foukemonsterworkshop/filming_accessories/DollyControl/MenuNavigation.ino

void interact_with_menu(MenuState state, int px, int py) {
  switch (state) {
    case MAIN:
      interact_main_menu(px, py);
      break;
    case HOME:
      interact_home_machine_menu(px, py);
      break;
    case JOG:
      interact_jog_menu(px, py);
      break;
    case VALUE_ENTRY:
      interact_data_input(px, py);
      break;
    default:
      interact_stand_in_menu(px, py);
  }
}

boolean is_pressed(int px, int py, int x, int y, int x1, int y1) {
  return px > x && px < x1 && py > y && py < y1;
}

void check_home_button(int px, int py) {
  int x = lcd.Get_Width() - 30;
  int y = lcd.Get_Height() - 30;

  if (is_pressed(px, py, x - 30, y - 30, x + 30, y + 30)) {
    requires_redraw = true;
    current_state = MAIN;
  }
}

void interact_stand_in_menu(int px, int py) {

  int border = 5;
  int selection_height = 30;
  int xOffset = lcd.Get_Display_Width() - border;
  int width = lcd.Get_Display_Width() - (2 * border);

  int list_position = 0;
  int display_position = 1;

  int labelXOffset = 2 * border;
  int labelYOffset = 12;

  check_home_button(px, py);

  if (is_pressed(px, py,
                 border,
                 (display_position * border) + (list_position * selection_height),
                 xOffset,
                 display_position * (border + selection_height))) {
    requires_redraw = true;
    current_state = MAIN;
  }
}
