foukemonsterworkshop/filming_accessories/DollyControl/MenuEnums.h

enum MenuState { MAIN,
                 HOME,
                 JOG,
                 PAN,
                 TRUCK,
                 PARALLAX,
                 VALUE_ENTRY };

enum Unit { INCH,
            CENTIMETER,
            ANGLE,
            SECOND,
            MINUTE };

enum STEPPER_FOCUS { GANTRY_M,
                     PAN_M };

enum STEPPER_INPUT { SPEED,
                     UNIT,
                     DURATION };
