foukemonsterworkshop/filming_accessories/DollyControl/ScreenDefinitions.h

//paramters define
#define MODEL ILI9341
#define CS   A5    
#define CD   A3
#define RST  A4
#define LED  A0   //if you don't need to control the LED pin,you should set it to -1 and set it to 3.3V

//touch screen paramters define
#define TCS   45
#define TCLK  46
#define TDOUT 47
#define TDIN  48
#define TIRQ  49

// We have a status line for like, is FONA working
#define STATUS_X 10
#define STATUS_Y 65

#define BLACK        0x0000  /*   0,   0,   0 */
#define BLUE         0x001F  /*   0,   0, 255 */
#define RED          0xF800  /* 255,   0,   0 */
#define DARKRED      0xEA03
#define GREEN        0x07E0  /*   0, 255,   0 */
#define DARKGREEN    0xF7E0  
#define CYAN         0x07FF  /*   0, 255, 255 */
#define MAGENTA      0xF81F  /* 255,   0, 255 */
#define YELLOW       0xFFE0  /* 255, 255,   0 */
#define WHITE        0xFFFF  /* 255, 255, 255 */
#define NAVY         0x000F  /*   0,   0, 128 */
#define DARKGREEN    0x03E0  /*   0, 128,   0 */
#define DARKCYAN     0x03EF  /*   0, 128, 128 */
#define MAROON       0x7800  /* 128,   0,   0 */
#define PURPLE       0x780F  /* 128,   0, 128 */
#define OLIVE        0x7BE0  /* 128, 128,   0 */
#define LIGHTGREY    0xC618  /* 192, 192, 192 */
#define DARKGREY     0x7BEF  /* 128, 128, 128 */
#define ORANGE       0xFD20  /* 255, 165,   0 */
#define GREENYELLOW  0xAFE5  /* 173, 255,  47 */
#define PINK         0xF81F  /* 255,   0, 255 */
